orion-campos/Touch_Media/3D/TouchMedia_3Dparts.png

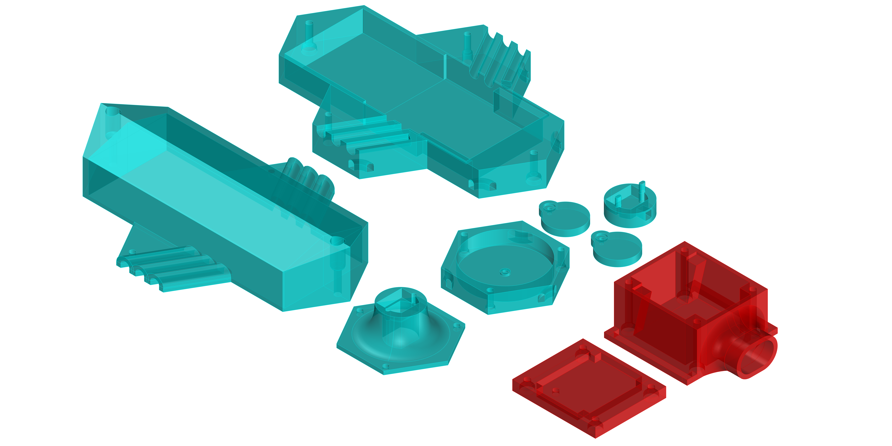
3D/TouchMedia_3Dparts.png
