orion-campos/Touch_Media/3D/TouchMedia_3Dparts_.png

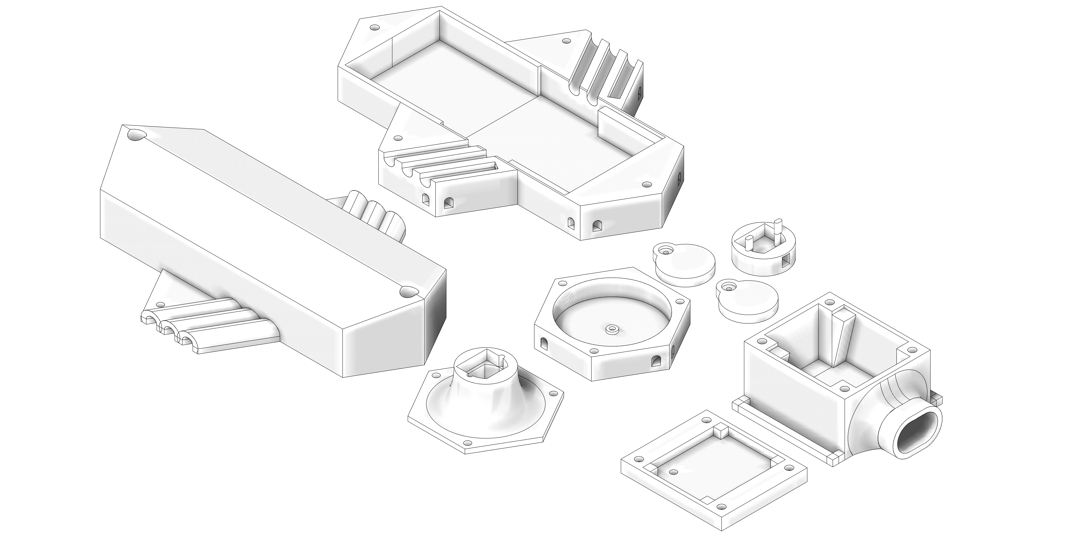
3D/TouchMedia_3Dparts_.png
