orion-campos/Touch_Media/ARDUINO_3_flex_sensors_dc_motors/flex_sensor_connection2.png

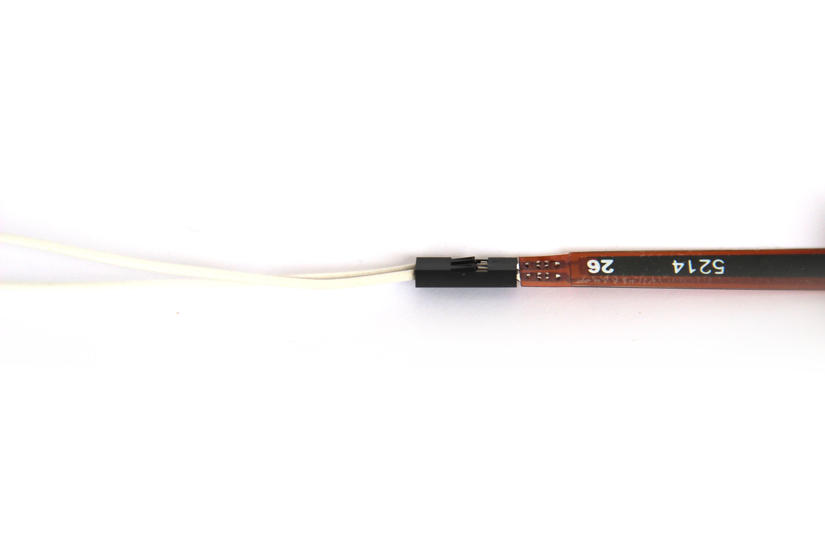
ARDUINO_3_flex_sensors_dc_motors/flex_sensor_connection2.png
