orion-campos/Touch_Media/CONCEPT/1.jpg

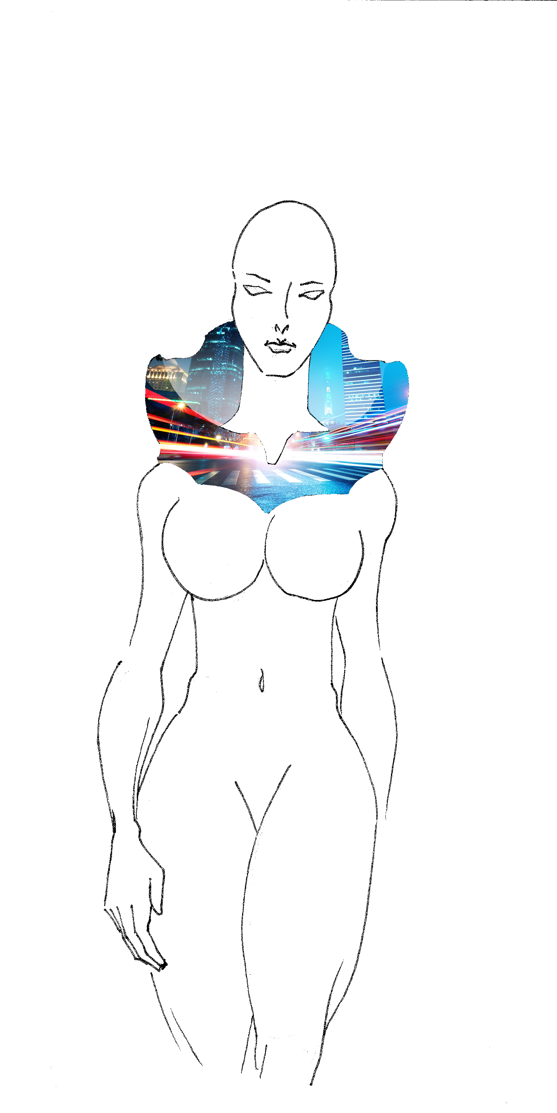
CONCEPT/1.jpg
