orion-campos/Touch_Media/CONCEPT/2.jpg

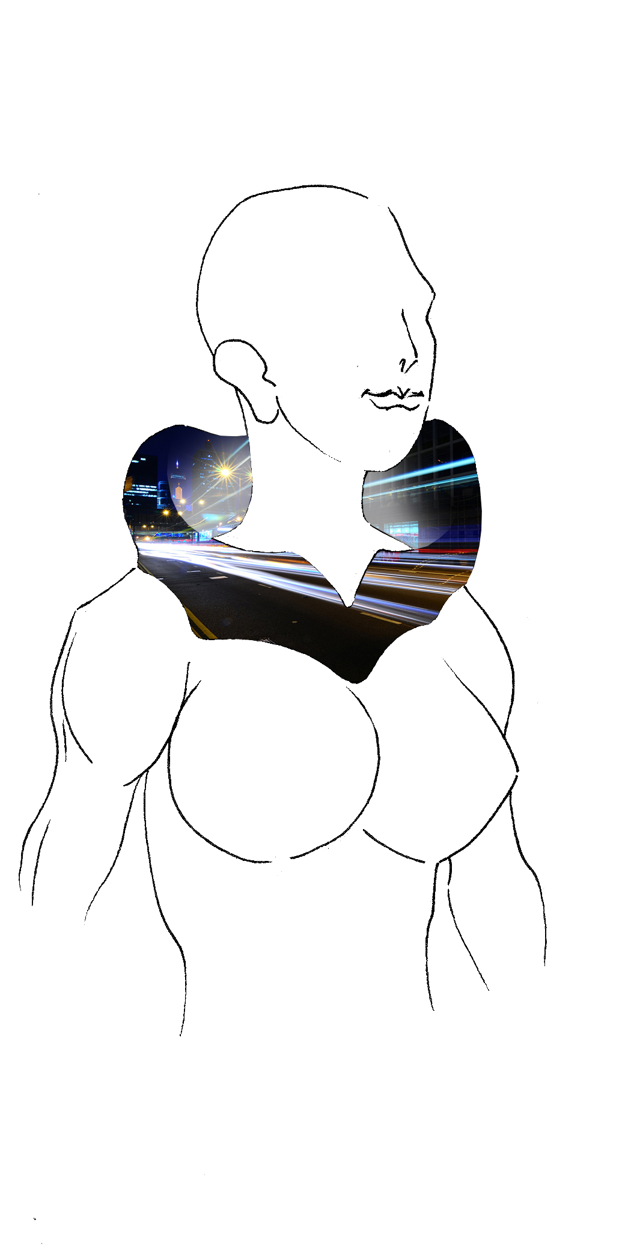
CONCEPT/2.jpg
