orion-campos/Touch_Media/CONCEPT/3.jpg

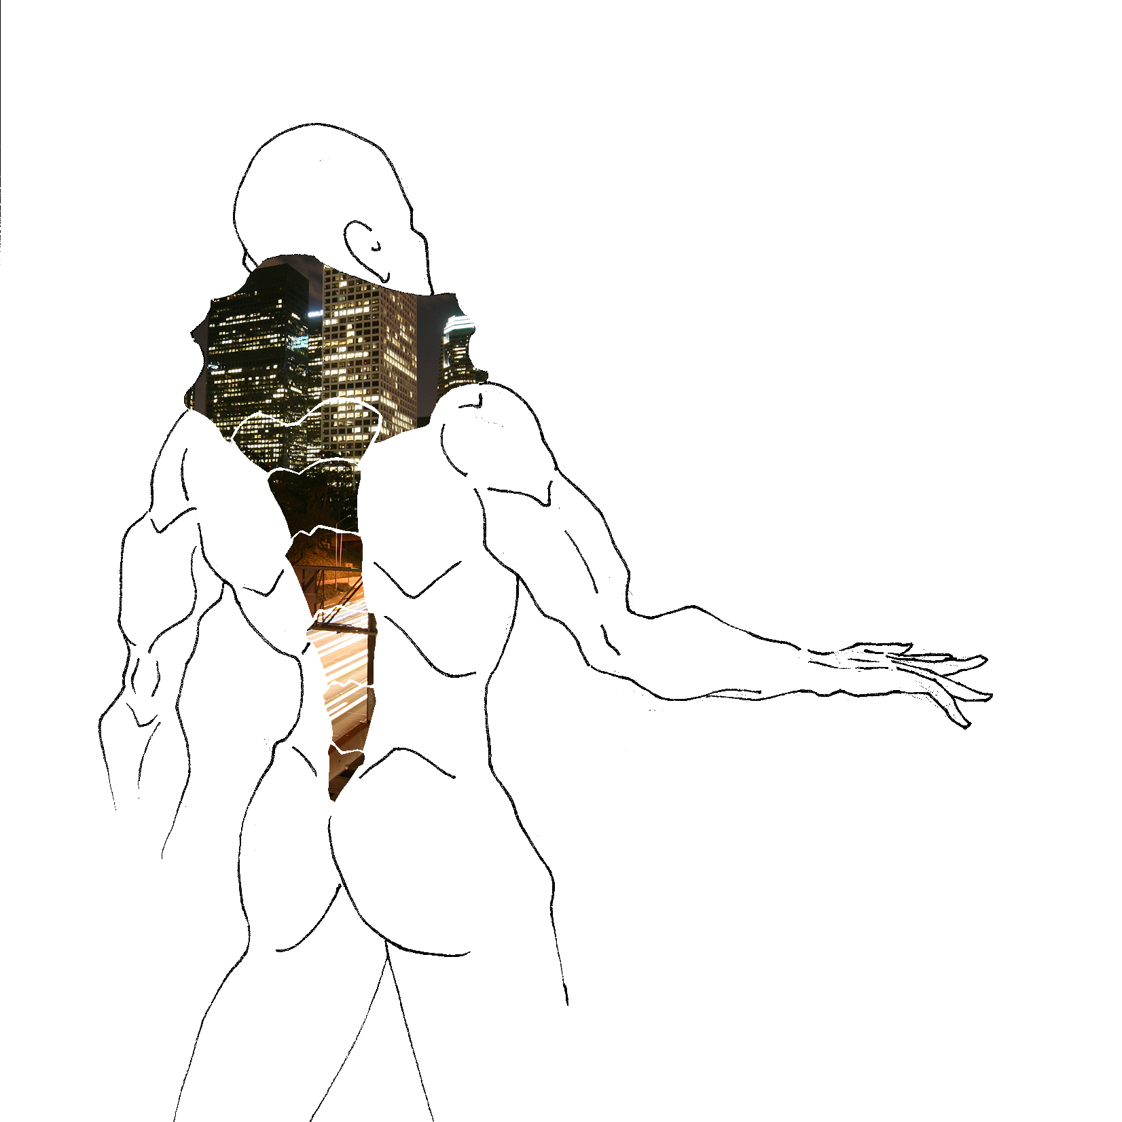
CONCEPT/3.jpg
