orion-campos/Touch_Media/EAGLE_PCBmilling/back/back_holes.png

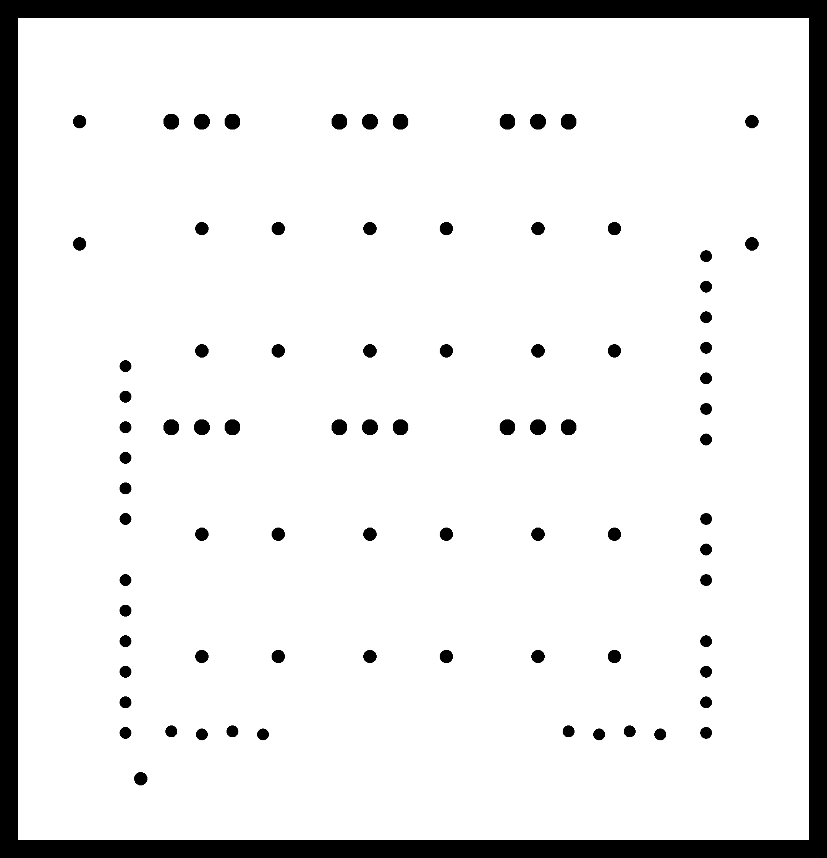
EAGLE_PCBmilling/back/back_holes.png
