orion-campos/Touch_Media/EAGLE_PCBmilling/back/back_path.png

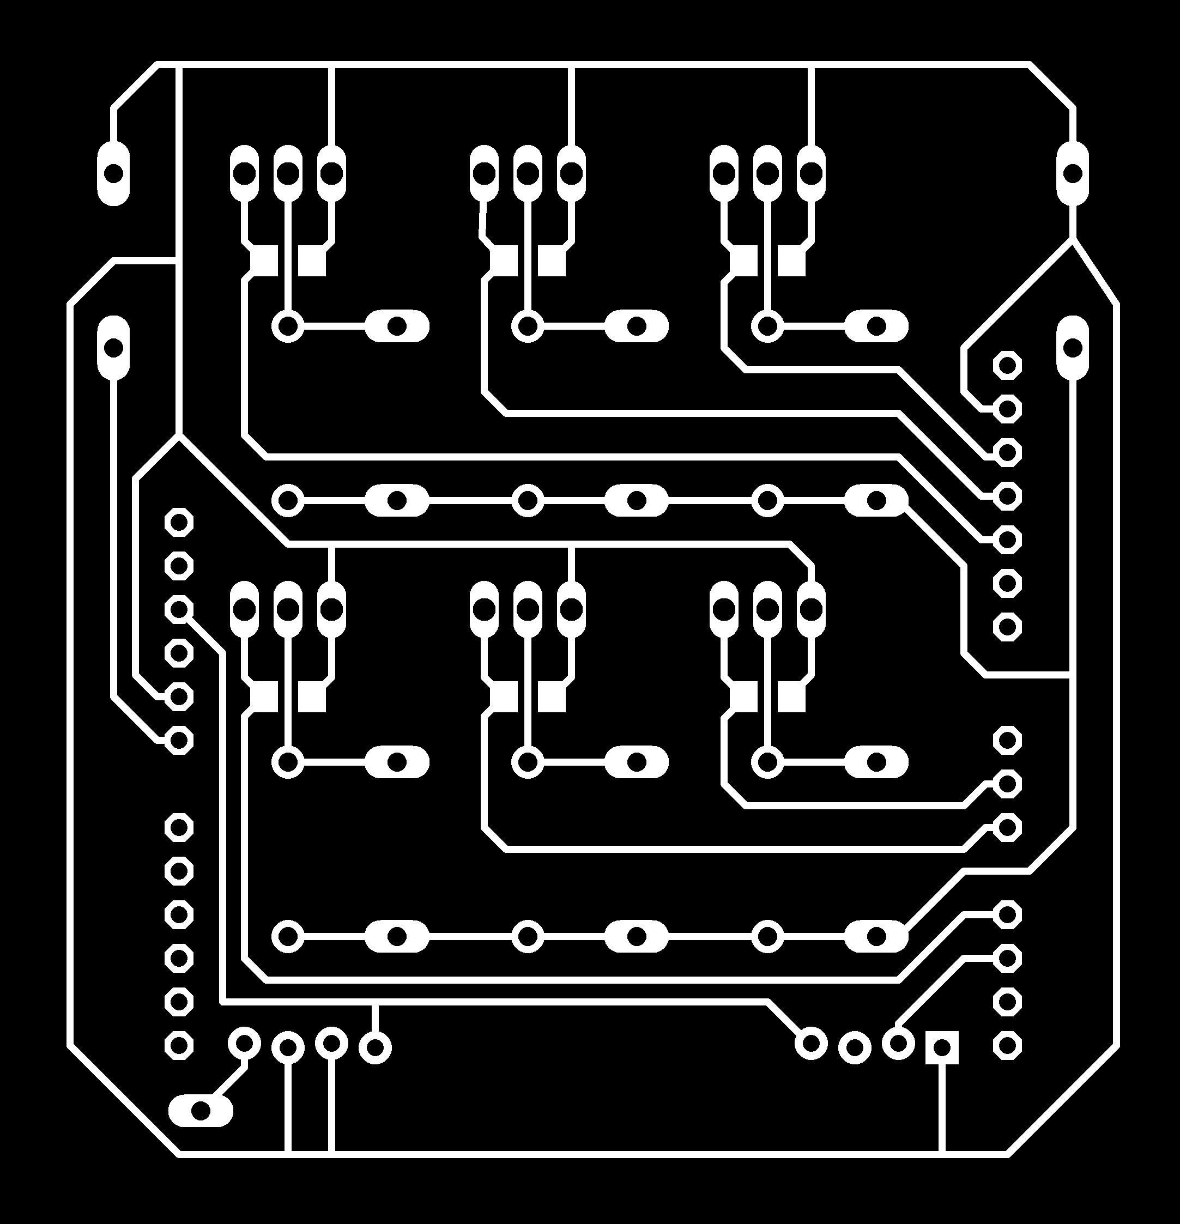
EAGLE_PCBmilling/back/back_path.png
