orion-campos/Touch_Media/EAGLE_PCBmilling/glove/glove_r5_holes.png

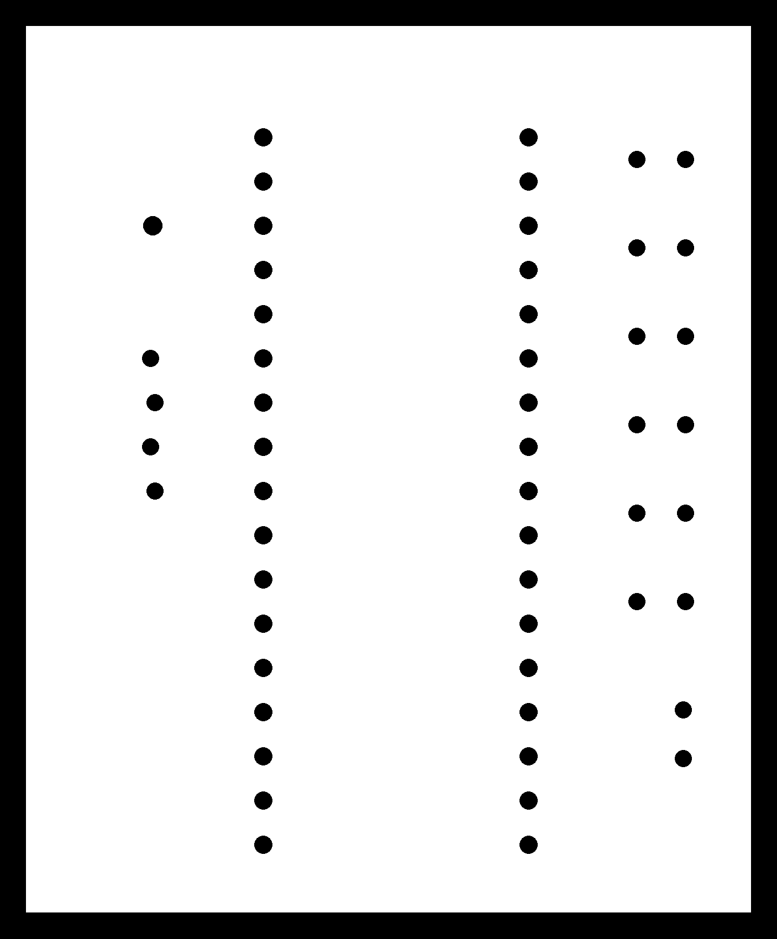
EAGLE_PCBmilling/glove/glove_r5_holes.png
